dg1vs/Transputer-TRAM-TangNano/hardware/docu_extern/IMG_7628.jpg

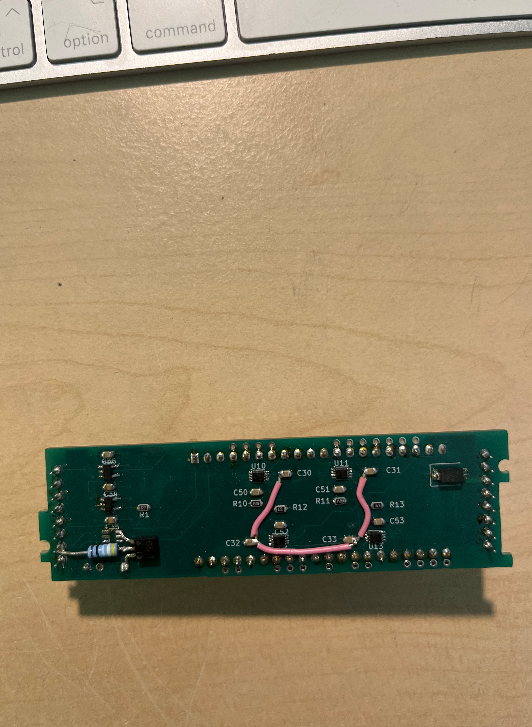
hardware/docu_extern/IMG_7628.jpg
